k12ish/SF4-Data-Logger/hardware/simulation/instrumentation amplifier.asc

22k: res; 22k
C1: cap; 2.2n
C2: cap; 2.2n
R1: res; 2.7k
R2: res; 8.2k
R3: res; 8.2k
R4: res; 1k
R5: res; 2.7k
R6: res; 22k
R7: res; 22k
R8: res; 22k
R9: res; 2.5k
R10: res; 1000k
R11: res; 1000k
R12: res; 470k
R13: res; 1000k
R14: res; 2.7k
U1: OP191
U2: OP191
U3: OP191
U4: OP191
U5: OP191
V1: voltage; 5
V2: voltage; SINE(0 0.08 20)
V3: voltage; 5
Named nets: +5V, -5V, 0
.tran 0.07
