k12ish/SF4-Data-Logger/hardware/simulation/averaging buffers.asc

U1: OP191
U2: OP191
U3: OP191
U4: OP191
U5: OP191
U6: OP191
V1: voltage; 10
V2: voltage; SINE(0 0.02 60); Rser=100k
V3: voltage; SINE(0 0.025 45); Rser=100k
V4: voltage; SINE(0 0.03 55); Rser=100k
Named nets: 0, +5V
.tran 0.5
003
002
006
